Covesh/SCARA-4DOF-Did-tico/Estrutura Mecânica/MG996R Servo Motor/Rubber Wire Cable Sleeve.SLDPRT

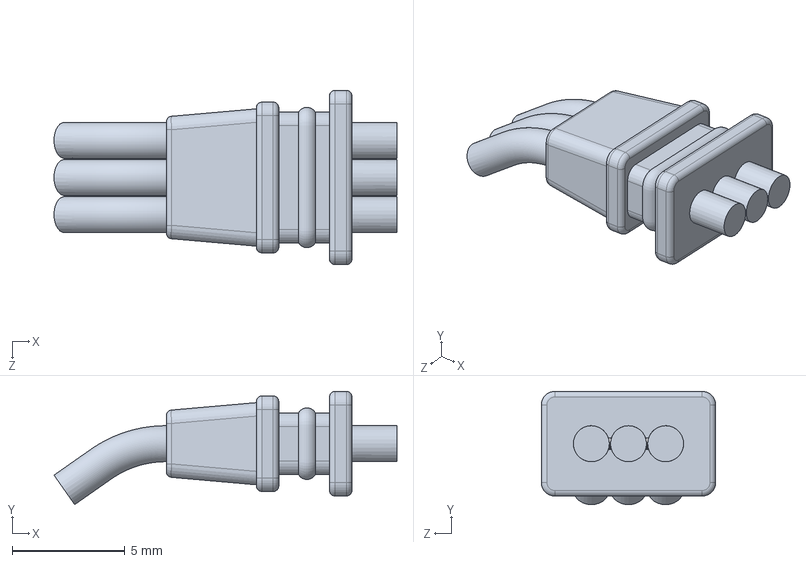
[picture p23: CAD file, 2025-07-21]
Estrutura Mecânica/MG996R Servo Motor/Rubber Wire Cable Sleeve.SLDPRT
15.2 x 5.03 x 7.75 mm
