Covesh/SCARA-4DOF-Did-tico/Estrutura Mecânica/DXF files/3ELO.dxf

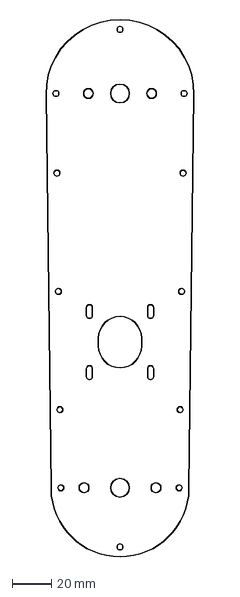
[picture p24: CAD file, 2025-07-21]
Estrutura Mecânica/DXF files/3ELO.dxf
75.3 x 274.2 mm
