Covesh/SCARA-4DOF-Did-tico/Estrutura Mecânica/MG996R Servo Motor/Servo Horns.SLDPRT

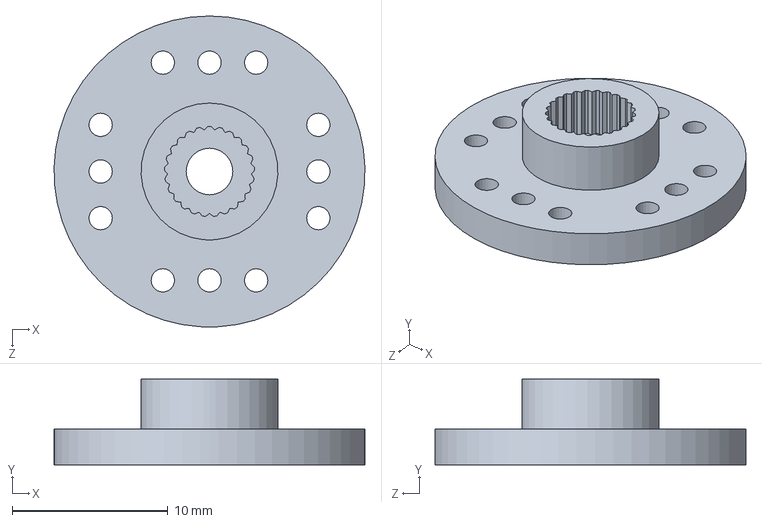
[picture p25: CAD file, 2025-07-21]
Estrutura Mecânica/MG996R Servo Motor/Servo Horns.SLDPRT
20.0 x 5.50 x 20.0 mm
