Covesh/SCARA-4DOF-Did-tico/Estrutura Mecânica/DXF files/Topo.dxf

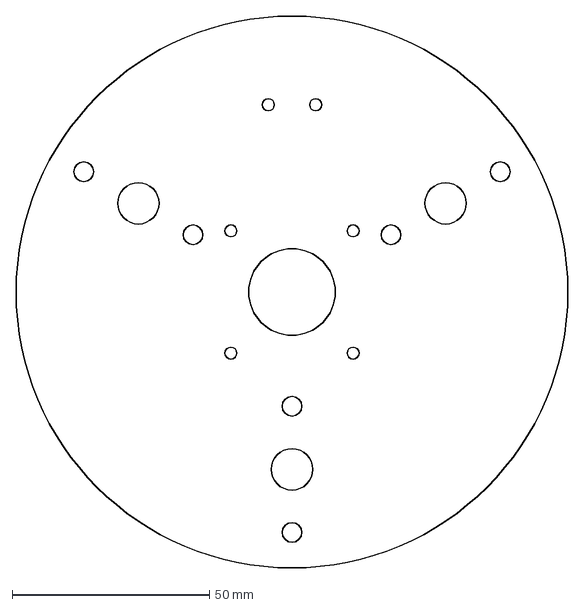
[picture p26: CAD file, 2025-07-21]
Estrutura Mecânica/DXF files/Topo.dxf
140.0 x 140.0 mm
