Covesh/SCARA-4DOF-Did-tico/Estrutura Mecânica/Limit switch/steel.STEP

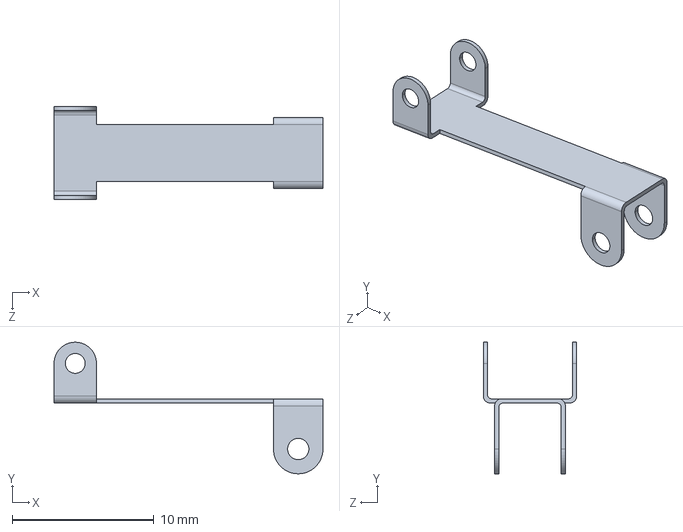
[picture p27: CAD file, 2025-07-21]
Estrutura Mecânica/Limit switch/steel.STEP
19.0 x 9.30 x 6.60 mm
